gary600/6502fb/software-sim/src/cpu/mod.rs

#![allow(unused)]

pub mod instruction;

use instruction::Instruction;

pub use instruction::Arch;
pub use instruction::instructions::create_arch;

pub trait CpuContext {
    fn read(&mut self, addr: u16) -> u8;
    fn read_immut(&self, addr: u16) -> u8;
    fn write(&mut self, addr: u16, val: u8);
}

pub enum State {
    Reset,
    Irq,
    Nmi,
    Run,
}

pub struct Cpu {
    pub status: u8,
    pub pc: u16,
    pub acc: u8,
    pub x: u8,
    pub y: u8,
    pub sp: u8,
    pub state: State,
    pub cycle: u64,
}

impl Cpu {
    pub fn new() -> Cpu {
        Cpu {
            status: 0,
            pc: 0xFFFC,
            acc: 0,
            x: 0,
            y: 0,
            sp: 0,
            state: State::Reset,
            cycle: 0,
        }
    }

    fn set_status(&mut self, v: bool, b: u8) {
        assert!(b < 8);
        self.status &= !(1 << b);
        self.status |= (v as u8) << b;
    }

    fn get_status(&self, b: u8) -> bool {
        (self.status >> b) & 1 != 0
    }

    pub fn read<Ctx: CpuContext>(&self, addr: u16, context: &mut Ctx) -> u8 {
        context.read(addr)
    }

    pub fn write<Ctx: CpuContext>(&mut self, addr: u16, value: u8, context: &mut Ctx) {
        context.write(addr, value);
    }

    pub fn set_decimal(&mut self, v: bool) {
        self.set_status(v, 3);
    }

    pub fn get_decimal(&self) -> bool {
        self.get_status(3)
    }

    pub fn set_interrupt(&mut self, v: bool) {
        self.set_status(v, 2);
    }

    pub fn get_interrupt(&self) -> bool {
        self.get_status(2)
    }

    pub fn set_neg(&mut self, v: bool) {
        self.set_status(v, 7);
    }

    pub fn get_neg(&self) -> bool {
        self.get_status(7)
    }

    pub fn set_overflow(&mut self, v: bool) {
        self.set_status(v, 6);
    }

    pub fn get_overflow(&self) -> bool {
        self.get_status(6)
    }

    pub fn set_carry(&mut self, v: bool) {
        self.set_status(v, 0);
    }

    pub fn get_carry(&self) -> bool {
        self.get_status(0)
    }

    pub fn set_zero(&mut self, v: bool) {
        self.set_status(v, 1);
    }

    pub fn get_zero(&self) -> bool {
        self.get_status(1)
    }

    pub fn read_wide_nowrap<Ctx: CpuContext>(&self, addr: u16, ctx: &mut Ctx) -> u16 {
        (self.read(addr + 1, ctx) as u16) << 8 | self.read(addr, ctx) as u16
    }

    pub fn read_wide<Ctx: CpuContext>(&self, addr: u16, ctx: &mut Ctx) -> u16 {
        let page = addr & 0xFF00;
        let idx = (addr as u8).wrapping_add(1) as u16;
        let addr_next = page | idx;
        (self.read(addr_next, ctx) as u16) << 8 | self.read(addr, ctx) as u16
    }

    pub fn push<Ctx: CpuContext>(&mut self, value: u8, ctx: &mut Ctx) {
        let old_sp = self.sp;
        self.write(0x0100 + old_sp as u16, value, ctx);
        self.sp = old_sp.wrapping_sub(1);
    }

    pub fn pop<Ctx: CpuContext>(&mut self, ctx: &mut Ctx) -> u8 {
        self.sp = self.sp.wrapping_add(1);
        self.read(0x0100 + self.sp as u16, ctx)
    }

    pub fn update_flags(&mut self, value: u8) {
        self.set_neg(value & (1 << 7) != 0);
        self.set_zero(value == 0);
    }

    pub fn trigger_nmi<Ctx: CpuContext>(&mut self, ctx: &mut Ctx) {
        self.push((self.pc >> 8) as u8, ctx);
        self.push((self.pc & 0xFF) as u8, ctx);
        self.push(self.status | 0b10 << 4, ctx);

        // Disable interrupts
        self.set_interrupt(true);

        self.pc = (self.read(0xFFFB, ctx) as u16) << 8 | self.read(0xFFFA, ctx) as u16;
        self.state = State::Nmi;

        self.cycle += 7;

        //println!("NMI triggered, PC is now {:#06X} ({:#04X})", self.pc, self.read(self.pc, ctx));
    }

    pub fn try_irq<Ctx: CpuContext>(&mut self, ctx: &mut Ctx) -> bool {
        if self.get_interrupt() {
            return false;
        }

        self.push((self.pc >> 8) as u8, ctx);
        self.push((self.pc & 0xFF) as u8, ctx);
        self.push(self.status | 0b10 << 4, ctx);

        // Disable interrupts
        self.set_interrupt(true);

        self.pc = (self.read(0xFFFF, ctx) as u16) << 8 | self.read(0xFFFE, ctx) as u16;
        self.state = State::Irq;

        true
    }

    pub fn print_stack<Ctx: CpuContext>(&self, ctx: &Ctx) {
        println!("SP: {:#04X}, Stack:", self.sp);
        for i in (self.sp as u16)..=255u16 {
            println!("{:#04X}: {:#04X}", i, ctx.read_immut(0x0100u16 + i));
        }
    }

    pub fn print_instr<Ctx: CpuContext>(&mut self, instr: &Instruction<Ctx>, ctx: &mut Ctx) {
        print!(
            "[PC: {:#06X}] A:{:02X} X:{:02X} Y:{:02X} P:{:02X} SP:{:02X} {} {: >4?}:",
            self.pc, self.acc, self.x, self.y, self.status, self.sp, instr.opcode, instr.mode
        );
        for i in 0..instr.mode.size() {
            print!("{:#04X} ", self.read(self.pc + i as u16, ctx));
        }
        println!();
    }

    pub fn next<Ctx: CpuContext>(&mut self, ctx: &mut Ctx, arch: &Arch<'_, Ctx>) -> usize {
        let cycles_taken = self.next_inner(ctx, arch);
        self.cycle += cycles_taken as u64;
        cycles_taken
    }

    fn next_inner<Ctx: CpuContext>(&mut self, ctx: &mut Ctx, arch: &Arch<'_, Ctx>) -> usize {
        match self.state {
            State::Reset => {
                self.pc =
                    (self.read(self.pc + 1, ctx) as u16) << 8 | self.read(self.pc, ctx) as u16;
                println!("Reset vector was {:#06X}", self.pc);
                self.state = State::Run;
                1
            }
            State::Irq | State::Nmi | State::Run => {
                let id = self.read(self.pc, ctx);
                let instr = arch[id as usize].as_ref().unwrap_or_else(|| {
                    self.print_stack(ctx);
                    panic!("Instruction {:#04X} does not exist", id)
                });

                // self.print_instr(instr, ctx);

                // TODO: Fix this
                if id == 0x00 && self.try_irq(ctx) {
                    1
                } else {
                    instr.run(ctx, self)
                }
            }
        }
    }
}

impl Default for Cpu {
    fn default() -> Cpu {
        Cpu::new()
    }
}
